embarquech/cryptnox-pos/main/ota_version.h

/*
 * SPDX-License-Identifier: LGPL-3.0-or-later
 * Copyright (c) 2026 Cryptnox SA
 */

/**
 * @file ota_version.h
 * @ingroup device
 * @brief Dotted version comparison, for deciding whether an update goes
 *        forwards or backwards.
 *
 * Header-only and free of ESP-IDF dependencies on purpose, the same reason
 * form_parse.h is: the answer decides what the panel tells the operator before
 * they replace the firmware on a terminal that signs transactions, and a
 * downgrade that gets announced as an upgrade is the failure that matters. Kept
 * where a host test can reach it (tests/units/test_ota_version.cpp).
 *
 * Deliberately NOT semver. Build metadata, pre-release tags and `git describe`
 * suffixes are ignored rather than ordered — "1.2.3-rc1" compares equal to
 * "1.2.3". Ordering release candidates is not a decision this device needs to
 * make, and the operator confirms every install on the panel regardless.
 */

#ifndef OTA_VERSION_H
#define OTA_VERSION_H

#include <stdbool.h>
#include <stddef.h>
#include <stdio.h>

/** @brief Numeric components compared; the rest of the string is ignored. */
#define OTA_VERSION_PARTS  4U

/** @brief Longest version string looked at, matching esp_app_desc_t::version. */
#define OTA_VERSION_MAX    32U
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
